saminkumra/Gest/hardware/3D_CAD/enclosure4_button.stl

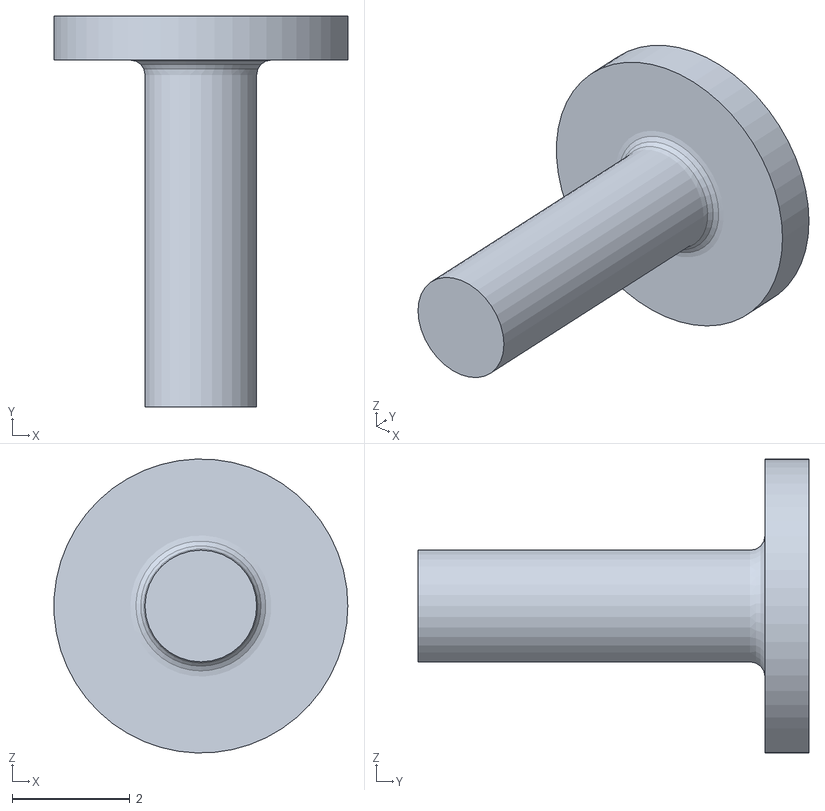
[picture p18: CAD file, 2022-08-04]
hardware/3D_CAD/enclosure4_button.stl
5.00 x 6.65 x 5.00
