saminkumra/Gest/Software/Gest/button_handler.ino

 /* ~~~~~~~~~~ INCLUDES ~~~~~~~~~~ */
#include "button_handler.h"
/*
void button_setup(){
  button_a.init(BUTTON);

  button_a.press_handler = a_press_handler;
}

void button_loop() {
  button_a.timingHandler();
}

void a_press_handler() {
  Serial.println("button works!!!");
}
*/
