saminkumra/Gest/Software/Two Hand Testing/BLE_Server_2/BLE_Server_2.ino

#include <BLEDevice.h>
#include <BLEServer.h>
#include <BLEUtils.h>
#include <BLE2902.h>

//BLE server name
#define bleServerName "Gest BLE-Server-1"

uint8_t user_button;
uint32_t user_time;

// Timer variables
unsigned long lastTime = 0;
unsigned long timerDelay = 30000;

bool deviceConnected = false;

#define SERVICE_UUID "d1ca45e2-3fea-4d55-9385-85919a7aecda"

BLECharacteristic gestButtonCharacteristic("f78ebbff-c8b7-4107-93de-889a6a06d408", BLECharacteristic::PROPERTY_NOTIFY);
BLEDescriptor bmeTemperatureFahrenheitDescriptor(BLEUUID((uint16_t)0x2902));

// Humidity Characteristic and Descriptor
BLECharacteristic gestTimeCharacteristic("ca73b3ba-39f6-4ab3-91ae-186dc9577d99", BLECharacteristic::PROPERTY_NOTIFY);
BLEDescriptor bmeHumidityDescriptor(BLEUUID((uint16_t)0x2903));

//Setup callbacks onConnect and onDisconnect
class MyServerCallbacks: public BLEServerCallbacks {
  void onConnect(BLEServer* pServer) {
    deviceConnected = true;
  };
  void onDisconnect(BLEServer* pServer) {
    deviceConnected = false;
  }
};


void setup() {
  // Start serial communication 
  Serial.begin(115200);

  // Create the BLE Device
  BLEDevice::init(bleServerName);

  // Create the BLE Server
  BLEServer *pServer = BLEDevice::createServer();
  pServer->setCallbacks(new MyServerCallbacks());

  // Create the BLE Service
  BLEService *bmeService = pServer->createService(SERVICE_UUID);

  // Create BLE Characteristics and Create a BLE Descriptor
  // Temperature
  #ifdef temperatureCelsius
    bmeService->addCharacteristic(&bmeTemperatureCelsiusCharacteristics);
    bmeTemperatureCelsiusDescriptor.setValue("BME temperature Celsius");
    bmeTemperatureCelsiusCharacteristics.addDescriptor(&bmeTemperatureCelsiusDescriptor);
  #else
    bmeService->addCharacteristic(&bmeTemperatureFahrenheitCharacteristics);
    bmeTemperatureFahrenheitDescriptor.setValue("BME temperature Fahrenheit");
    bmeTemperatureFahrenheitCharacteristics.addDescriptor(&bmeTemperatureFahrenheitDescriptor);
  #endif  

  // Humidity
  bmeService->addCharacteristic(&bmeHumidityCharacteristics);
  bmeHumidityDescriptor.setValue("BME humidity");
  bmeHumidityCharacteristics.addDescriptor(new BLE2902());
  
  // Start the service
  bmeService->start();

  // Start advertising
  BLEAdvertising *pAdvertising = BLEDevice::getAdvertising();
  pAdvertising->addServiceUUID(SERVICE_UUID);
  pServer->getAdvertising()->start();
  Serial.println("Waiting a client connection to notify...");
}

void loop() {
  if (deviceConnected) {
    if ((millis() - lastTime) > timerDelay) {
      // Read temperature as Celsius (the default)
      temp = bme.readTemperature();
      // Fahrenheit
      tempF = 1.8*temp +32;
      // Read humidity
      hum = bme.readHumidity();
  
      //Notify temperature reading from BME sensor
      #ifdef temperatureCelsius
        static char temperatureCTemp[6];
        dtostrf(temp, 6, 2, temperatureCTemp);
        //Set temperature Characteristic value and notify connected client
        bmeTemperatureCelsiusCharacteristics.setValue(temperatureCTemp);
        bmeTemperatureCelsiusCharacteristics.notify();
        Serial.print("Temperature Celsius: ");
        Serial.print(temp);
        Serial.print(" ºC");
      #else
        static char temperatureFTemp[6];
        dtostrf(tempF, 6, 2, temperatureFTemp);
        //Set temperature Characteristic value and notify connected client
        bmeTemperatureFahrenheitCharacteristics.setValue(temperatureFTemp);
        bmeTemperatureFahrenheitCharacteristics.notify();
        Serial.print("Temperature Fahrenheit: ");
        Serial.print(tempF);
        Serial.print(" ºF");
      #endif
      
      //Notify humidity reading from BME
      static char humidityTemp[6];
      dtostrf(hum, 6, 2, humidityTemp);
      //Set humidity Characteristic value and notify connected client
      bmeHumidityCharacteristics.setValue(humidityTemp);
      bmeHumidityCharacteristics.notify();   
      Serial.print(" - Humidity: ");
      Serial.print(hum);
      Serial.println(" %");
      
      lastTime = millis();
    }
  }
}
