saminkumra/Gest/Software/Two Hand Testing/esp-now-receiver-BLE/twoHandReceiver.ino

#include "twoHandReceiver.h"

void twoHandReceiverInit(){
  // Set device as a Wi-Fi Station
  WiFi.mode(WIFI_STA);
  esp_wifi_set_mac(WIFI_IF_STA, &newMACAddress[0]);

  // Init ESP-NOW
  if (esp_now_init() != ESP_OK) {
    Serial.println("Error initializing ESP-NOW");
    return;
  }
  
  // Once ESPNow is successfully Init, we will register for recv CB to
  // get recv packer info
  esp_now_register_recv_cb(OnDataRecv);
}

void twoHandReceiverLoop(){
  Serial.print("Char: ");
  Serial.println((int)myData.button);
}

// callback function that will be executed when data is received
void OnDataRecv(const uint8_t * mac, const uint8_t *incomingData, int len) {
  memcpy(&myData, incomingData, sizeof(myData));
//  Serial.print("Char: ");
//  Serial.println((int)myData.button);
}
